hhawley/Charge-Injector/sym/charge_injector.asc

B1: bv; V=idt(V(Vout))
B2: bv; V=idt(V(VReal))
C1: cap; {Cc}
C2: cap; {Cc}
C3: cap; 3.3n
C4: cap; 100n
C5: cap; 1p
R1: res; {Rsupply}
R2: res; 10
R3: res; 1k
R4: res; 1k
R5: res; {Rload}
R6: res; {Rsupply}
R7: res; {Rload}
R8: res; 100Meg
R9: res; 50
U1: UniversalOpAmp
U2: AD8065
V1: voltage; PULSE(0 1 0 0 0 1000u 0 1); AC 1
V2: battery; 5
V3: battery; 5
V4: voltage; 1
Named nets: 0, Vout, Vcc, Vss, VReal, Qmeas, Qreal
;tran 0 2u 0 100p
.param Cc=9.1p Rload=49.9 Rsupply=1
V4 to be designed with a voltage reference: 
value does not matter as long as it is between
the rails of U2
Generic DC blocking. Not in the final design
Cc 9.1p is the highest precision NPO
I can find (0.5%)
High C3 required: min(vout) must be below 0.5V
but not too big the pulse tail is longer than 5us
(max digitizer waveform)
;noise V(Vout) V1 dec 10 10 20Meg
Input stage meant to be a high-precision relay-based 
square wave of 1Vpp
SNR = 2.1mV /  28.057µV = 75 (peak value over std)
.ac dec 50 10 200Meg
